nehajaykul/analog-mixer/ltspice/Full_Mixer.asc

C1: cap; 100n
C2: cap; 100n
C3: cap; 10n
C4: cap; 10n
C5: cap; 470n
C6: cap; 470n
C7: cap; 470n
C8: cap; 470n
C9: cap; 100n
C10: cap; 100n
C11: cap; 10n
C12: cap; 10n
C17: cap; 100n
C18: cap; 100n
C19: cap; 100n
C20: cap; 100n
D3: diode
D6: diode
neg_rail: voltage; 15
pos_rail: voltage; 15
R1: res; 8.2K; tol=1
R2: res; 8.2K; tol=1
R3: res; 10K; tol=1
R4: res; 10K; tol=1
R5: res; 10K; tol=1
R6: res; 5K; tol=1
R7: res; 10K; tol=1
R8: res; 10K; tol=1
R9: res; 3.9K; tol=1
R10: res; 3.9K; tol=1
R11: res; 10K; tol=1
R12: res; 10K; tol=1
R13: res; 10K; tol=1
R14: res; 10K; tol=1
R15: res; 6K; tol=1
R16: res; 10K; tol=1
R17: res; 28K; tol=1
R18: res; 28K; tol=1
R19: res; 28K; tol=1
R20: res; 28K; tol=1
R21: res; {50000*(1-low_a)}; tol=1
R22: res; {50000*low_a}; tol=1
R23: res; {50000*(1-band_a)}; tol=1
R24: res; {50000*band_a}; tol=1
R25: res; {50000*(1-high_a)}; tol=1
R26: res; {50000*high_a}; tol=1
R27: res; 3.3K; tol=1
R28: res; 10K; tol=1
R29: res; 10K; tol=1
R30: res; 390; tol=1
R31: res; {50000*(ch_a**2)}; tol=1
R32: res; {50000*(1-ch_a**2)}; tol=1
R33: res; 3.3K; tol=1
R34: res; 10K; tol=1
R35: res; {10000*(fade_a)}; tol=1
R36: res; {10000*(1-fade_a)}; tol=1
R37: res; 10K; tol=1
R38: res; 10K; tol=1
R39: res; 500; tol=1
R40: res; 100K; tol=1
R41: res; 8.2K; tol=1
R42: res; 8.2K; tol=1
R43: res; 10K; tol=1
R44: res; 10K; tol=1
R45: res; 10K; tol=1
R46: res; 10K; tol=1
R47: res; 5K; tol=1
R48: res; 10K; tol=1
R49: res; 3.9K; tol=1
R50: res; 3.9K; tol=1
R51: res; 10K; tol=1
R52: res; 10K; tol=1
R53: res; 10K; tol=1
R54: res; 10K; tol=1
R55: res; 6K; tol=1
R56: res; 10K; tol=1
R61: res; {50000*(1-low_b)}; tol=1
R62: res; {50000*low_b}; tol=1
R63: res; {50000*(1-band_b)}; tol=1
R64: res; {50000*band_b}; tol=1
R65: res; {50000*(1-high_b)}; tol=1
R66: res; {50000*high_b}; tol=1
R67: res; 10K; tol=1
R68: res; 10K; tol=1
R69: res; 3.3K; tol=1
R70: res; 3.3K; tol=1
R71: res; 10K; tol=1
R72: res; {50000*(ch_b**2)}; tol=1
R73: res; {50000*(1-ch_b**2)}; tol=1
R74: res; {10000*(fade_b)}; tol=1
R75: res; {10000*(1-fade_b)}; tol=1
R76: res; 390; tol=1
R77: res; 10K; tol=1
R78: res; 10K; tol=1
R79: res; 500; tol=1
R80: res; 100K; tol=1
R81: res; 100K; tol=1
R82: res; 100K; tol=1
R83: res; {10000*(cross)}; tol=1
R84: res; {10000*(1-cross)}; tol=1
R85: res; {10000*(cross)}; tol=1
R86: res; {10000*(1-cross)}; tol=1
R87: res; 10K; tol=1
R88: res; 10K; tol=1
R89: res; {50000*(master)}; tol=1
R90: res; {50000*(1-master)}; tol=1
R91: res; 10K; tol=1
R92: res; 100k; tol=1
R93: res; 10K; tol=1
R94: res; 47; tol=1
R95: res; 3.3K; tol=1
R96: res; 10K; tol=1
R99: res; {10000*(cfx_a)}; tol=1
R100: res; {10000*(1-cfx_a)}; tol=1
R101: res; {10000*(cfx_a)}; tol=1
R102: res; {10000*(1-cfx_a)}; tol=1
R103: res; 10K; tol=1
R104: res; 10K; tol=1
R107: res; {10000*(cfx_b)}; tol=1
R108: res; {10000*(1-cfx_b)}; tol=1
R109: res; {10000*(cfx_b)}; tol=1
R110: res; {10000*(1-cfx_b)}; tol=1
R111: res; 10K; tol=1
R112: res; 10K; tol=1
R113: res; 10K; tol=1
R114: res; 7.8K; tol=1
R115: res; {50000*(pfl**2)}; tol=1
R116: res; {50000*(1-pfl**2)}; tol=1
R117: res; 10K; tol=1
R118: res; 150
R122: res; 500; tol=1
track_a: voltage; ""; AC 1
track_b: voltage; ""; AC 1
U1: UniversalOpAmp2; Avol=200K GBW=10Meg Slew=9Meg; Ilimit=30m Rail=0
U2: UniversalOpAmp2; Avol=200K GBW=10Meg Slew=9Meg; Ilimit=30m Rail=0 Vos=0
U3: UniversalOpAmp2; Avol=200K GBW=10Meg Slew=9Meg; Ilimit=30m Rail=0 Vos=0
U4: UniversalOpAmp2; Avol=200K GBW=10Meg Slew=9Meg; Ilimit=30m Rail=0 Vos=0
U5: UniversalOpAmp2; Avol=200K GBW=10Meg Slew=9Meg; Ilimit=30m Rail=0
U6: UniversalOpAmp2; Avol=200K GBW=10Meg Slew=9Meg; Ilimit=30m Rail=0 Vos=0
U7: UniversalOpAmp2; Avol=200K GBW=10Meg Slew=9Meg; Ilimit=30m Rail=0 Vos=0
U8: UniversalOpAmp2; Avol=200K GBW=10Meg Slew=9Meg; Ilimit=30m Rail=0 Vos=0
U9: UniversalOpAmp2; Avol=200K GBW=10Meg Slew=9Meg; Ilimit=30m Rail=0
U10: UniversalOpAmp2; Avol=200K GBW=10Meg Slew=9Meg; Ilimit=30m Rail=0
U11: UniversalOpAmp2; Avol=200K GBW=10Meg Slew=9Meg; Ilimit=30m Rail=0 Vos=0
U12: UniversalOpAmp2; Avol=200K GBW=10Meg Slew=9Meg; Ilimit=30m Rail=0 Vos=0
U13: UniversalOpAmp2; Avol=200K GBW=10Meg Slew=9Meg; Ilimit=30m Rail=0 Vos=0
U14: UniversalOpAmp2; Avol=200K GBW=10Meg Slew=9Meg; Ilimit=30m Rail=0
U15: UniversalOpAmp2; Avol=200K GBW=10Meg Slew=9Meg; Ilimit=30m Rail=0 Vos=0
U16: UniversalOpAmp2; Avol=200K GBW=10Meg Slew=9Meg; Ilimit=30m Rail=0 Vos=0
U17: UniversalOpAmp2; Avol=200K GBW=10Meg Slew=9Meg; Ilimit=30m Rail=0 Vos=0
U18: UniversalOpAmp2; Avol=200K GBW=10Meg Slew=9Meg; Ilimit=30m Rail=0
U19: UniversalOpAmp2; Avol=200K GBW=10Meg Slew=9Meg; Ilimit=30m Rail=0 Vos=0
U20: UniversalOpAmp2; Avol=200K GBW=10Meg Slew=9Meg; Ilimit=30m Rail=0 Vos=0
U21: UniversalOpAmp2; Avol=200K GBW=10Meg Slew=9Meg; Ilimit=30m Rail=0 Vos=0
U24: UniversalOpAmp2; Avol=200K GBW=10Meg Slew=9Meg; Ilimit=30m Rail=0 Vos=0
U25: UniversalOpAmp2; Avol=200K GBW=10Meg Slew=9Meg; Ilimit=30m Rail=0 Vos=0
U26: UniversalOpAmp2; Avol=200K GBW=10Meg Slew=9Meg; Ilimit=30m Rail=0 Vos=0
U27: UniversalOpAmp2; Avol=200K GBW=10Meg Slew=9Meg; Ilimit=30m Rail=0 Vos=0
U28: UniversalOpAmp2; Avol=200K GBW=10Meg Slew=9Meg; Ilimit=30m Rail=0 Vos=0
U29: UniversalOpAmp2; Avol=200K GBW=10Meg Slew=9Meg; Ilimit=30m Rail=0 Vos=0
U30: UniversalOpAmp2; Avol=200K GBW=10Meg Slew=9Meg; Ilimit=30m Rail=0 Vos=0
U31: UniversalOpAmp2; Avol=200K GBW=10Meg Slew=9Meg; Ilimit=30m Rail=0 Vos=0
U32: UniversalOpAmp2; Avol=200K GBW=10Meg Slew=9Meg; Ilimit=30m Rail=0
U33: UniversalOpAmp2; Avol=200K GBW=10Meg Slew=9Meg; Ilimit=30m Rail=0
Named nets: 0, +15V, -15V, low_pass_a, band_pass_a, high_pass_a, low_pass_b, band_pass_b, high_pass_b, a_out, b_out, sum_out_b, sum_out_a, master_out, pfl_a, pfl_b, panel_mount_headphone_jack
PFL
TRACK A
TRACK B
SUMMING
