nehajaykul/analog-mixer/ltspice/Gain_and_Channel_Fader.asc

D1: diode
R1: res; {50000*(1-low_a)}; tol=1
R2: res; {50000*low_a}; tol=1
R3: res; {50000*(1-band_a)}; tol=1
R4: res; {50000*band_a}; tol=1
R5: res; {50000*(1-high_a)}; tol=1
R6: res; {50000*high_a}; tol=1
R7: res; 10K; tol=1
R8: res; 10K; tol=1
R9: res; 3.3K; tol=1
R10: res; 3.3K; tol=1
R11: res; 10K; tol=1
R12: res; {50000*(ch_a**2)}; tol=1
R13: res; {50000*(1-ch_a**2)}; tol=1
R14: res; {10000*(fade_a)}; tol=1
R15: res; {10000*(1-fade_a)}; tol=1
R16: res; 10K; tol=1
R17: res; 10K; tol=1
R18: res; 500; tol=1
R19: res; {10000*(cfx_a)}; tol=1
R20: res; {10000*(1-cfx_a)}; tol=1
R21: res; {10000*(cfx_a)}; tol=1
R22: res; {10000*(1-cfx_a)}; tol=1
R23: res; 10K; tol=1
R24: res; 10K; tol=1
R25: res; 390; tol=1
U1: UniversalOpAmp2; Avol=200K GBW=10Meg Slew=9Meg; Ilimit=30m Rail=0 Vos=0
U2: UniversalOpAmp2; Avol=200K GBW=10Meg Slew=9Meg; Ilimit=30m Rail=0 Vos=0
U3: UniversalOpAmp2; Avol=200K GBW=10Meg Slew=9Meg; Ilimit=30m Rail=0 Vos=0
Named nets: low_pass_a, band_pass_a, high_pass_a, 0, -15V, +15V, a_out, sum_out_a, pfl_a
