nehajaykul/analog-mixer/ltspice/PFL_Output.asc

R1: res; 10K; tol=1
R2: res; 10K; tol=1
R3: res; 7.8K; tol=1
R4: res; {50000*(pfl**2)}; tol=1
R5: res; {50000*(1-pfl**2)}; tol=1
R6: res; 10K; tol=1
R7: res; 500; tol=1
R8: res; 150
U1: UniversalOpAmp2; Avol=200K GBW=10Meg Slew=9Meg; Ilimit=30m Rail=0 Vos=0
U2: UniversalOpAmp2; Avol=200K GBW=10Meg Slew=9Meg; Ilimit=30m Rail=0 Vos=0
Named nets: pfl_b, pfl_a, 0, -15V, +15V, panel_mount_headphone_jack
