nehajaykul/analog-mixer/ltspice/Virtual_Earth_and _Master_Output.asc

R1: res; {10000*(cross)}; tol=1
R2: res; {10000*(1-cross)}; tol=1
R3: res; {10000*(cross)}; tol=1
R4: res; {10000*(1-cross)}; tol=1
R5: res; 10K; tol=1
R6: res; 10K; tol=1
R7: res; 10K; tol=1
R8: res; {50000*(master)}; tol=1
R9: res; {50000*(1-master)}; tol=1
R10: res; 100k; tol=1
R11: res; 47; tol=1
R12: res; 3.3K; tol=1
R13: res; 10K; tol=1
U1: UniversalOpAmp2; Avol=200K GBW=10Meg Slew=9Meg; Ilimit=30m Rail=0 Vos=0
U2: UniversalOpAmp2; Avol=200K GBW=10Meg Slew=9Meg; Ilimit=30m Rail=0 Vos=0
U3: UniversalOpAmp2; Avol=200K GBW=10Meg Slew=9Meg; Ilimit=30m Rail=0 Vos=0
Named nets: a_out, b_out, 0, -15V, +15V, master_out
